sparkfun/Sparkpunk/simulations/oscillators.asc

1meg: res; 100
C1: cap; 1µ
C2: cap; 0.47µ
C3: cap; 10µ
C4: cap; 10µ
C5: cap; 10µ
C6: cap; 10µ
D1: diode
D2: diode
R1: res; 10k
R2: res; 100k
R3: res; 100k
R4: res; 470
R5: res; 5k
R6: res; 10k
R7: res; 10k
R8: res; 10k
R9: res; 100k
R10: res; 100k
R11: res; 470
R12: res; 5k
R13: res; 10k
U1: NE555
U2: NE555
U3: CD4013B
U4: CD4013B
U5: UniversalOpamp2
V1: voltage; 9
V2: voltage; PULSE(0 9 2 1u 1u 1 1 1)
V3: voltage; PULSE(0 9 8 1u 1u 1 1 1)
Named nets: vdd, 0, vout
.tran 12
.inc CD4000_v.lib
Experiments with actual 7555 indicate that pulldown after diodes can be significantly larger.
