sparkfun/Sparkpunk/simulations/filter-compare.asc

C1: cap; 100n
C2: cap; 100n
C3: cap; 100n
C4: cap; 2µ
C5: cap; 100n
C6: cap; 500n
C7: cap; 500n
C8: cap; 500n
C9: cap; 500n
C10: cap; 1µ
C11: cap; .1µ
C12: cap; .1µ
R1: res; 5k
R2: res; 60k
R3: res; 5k
R4: res; {rv}
R5: res; {rv}
R6: res; {rv}
R7: res; 2k
R8: res; {rv}
R9: res; 10k
R10: res; 10k
R11: res; {rv}
R12: res; 1meg
R13: res; 27k
R14: res; 1meg
U1: UniversalOpamp2
U2: UniversalOpamp2
U3: UniversalOpamp2
U4: UniversalOpamp2
U5: UniversalOpamp2
V1: voltage; 12
V2: voltage; SINE(0 2 100 .5); AC ac 1.
V3: voltage; 12
Named nets: 0, v+, v-, vout, vout2, vout3, vout4, vout5
;tran 2
.ac oct 20 5 30000
.step param rv 10 10000 100
