sparkfun/Sparkpunk/simulations/sum-and-filter.asc

C1: cap; 10µ
C2: cap; 10µ
C3: cap; 10µ
C4: cap; 2µ
C5: cap; .1µ
C6: cap; 10µ
R1: res; 100k
R2: res; 10k
R3: res; 10k
R4: res; 10k
R5: res; 100k
R6: res; 100k
R7: res; {rv}
R8: res; {rv}
R9: res; 10k
U1: UniversalOpamp2
U2: UniversalOpamp2
V1: voltage; 12
V2: voltage; SINE(6 6 100 .5); AC ac 1.
Named nets: 0, v+, vout2, vref
;tran 2
.ac oct 10 1 100000
.step param rv 10 10000 200
